terriblefire/tfpcmcia/firmware/User/ch32v4x7_it.c

#include "ch32v4x7_it.h"

void NMI_Handler(void) __attribute__((interrupt("WCH-Interrupt-fast")));
void HardFault_Handler(void) __attribute__((interrupt("WCH-Interrupt-fast")));

void NMI_Handler(void) {
    while (1) {}
}

void HardFault_Handler(void) {
    while (1) {}
}
